orgasms4worldpeace/mk312-bt/1-order-boards/schematics/pages/v1.4 Schematic Page 2.png

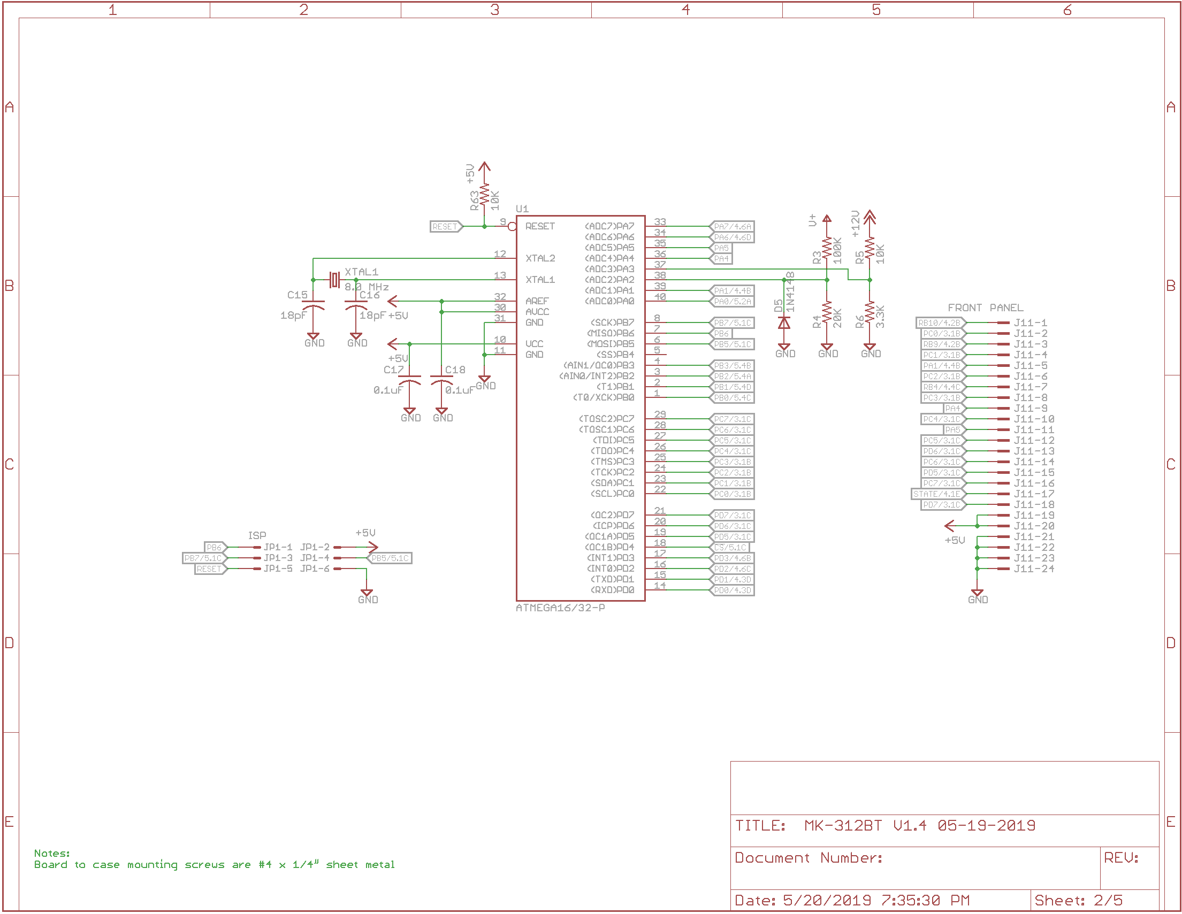
1-order-boards/schematics/pages/v1.4 Schematic Page 2.png
